ThertyOne/straznik-ksiazek/sym_konwertery_napiec_logicznych.asc

R1: res; 10k
R2: res; 10k
R3: res; 1k
R4: res; 1k
R5: res; 1k
U1: BSS138_ZTX
V1: voltage; PULSE(0 3.3 0 0 0 0.2 0.4)
V2: voltage; 5
V3: voltage; 3.3
V4: voltage; PULSE(0 5 0 0 0 0.2 0.4)
Named nets: 0, 5V, 3.3_sig, out_5, 3.3V, 5_sig, out
.tran 2
